afonsus1997/Q-Dice/Software/Qdice-main/Core/Inc/retarget.h

// All credit to Carmine Noviello for this code
// https://github.com/cnoviello/mastering-stm32/blob/master/nucleo-f030R8/system/include/retarget/retarget.h

#ifndef _RETARGET_H__
#define _RETARGET_H__

#include "stm32l0xx_hal.h"
#include <sys/stat.h>

void RetargetInit(UART_HandleTypeDef *huart);
//int _isatty(int fd);
int _write(int fd, char* ptr, int len);
//int _close(int fd);
//int _lseek(int fd, int ptr, int dir);
int _read(int fd, char* ptr, int len);
//int _fstat(int fd, struct stat* st);

#endif //#ifndef _RETARGET_H__
